kasom/EPOBD2ESP32U8G2/AutoPollingMessages.h

#define NUM_AUTO_POLLING_CAN_MESSAGES 13

can_message_t auto_polling_messages[NUM_AUTO_POLLING_CAN_MESSAGES] = {
  {.flags=0, .identifier=BMS_ID, .data_length_code=8, .data={0x03,0x22,0xb0,0x42,0xaa,0xaa,0xaa,0xaa}}, // HV A
  {.flags=0, .identifier=BMS_ID, .data_length_code=8, .data={0x03,0x22,0xb0,0x43,0xaa,0xaa,0xaa,0xaa}}, // HV V
  {.flags=0, .identifier=BMS_ID, .data_length_code=8, .data={0x03,0x22,0xb0,0x46,0xaa,0xaa,0xaa,0xaa}}, // SoC
  {.flags=0, .identifier=BMS_ID, .data_length_code=8, .data={0x03,0x22,0xb0,0x48,0xaa,0xaa,0xaa,0xaa}}, // Charging status
  {.flags=0, .identifier=BMS_ID, .data_length_code=8, .data={0x03,0x22,0xb0,0x5c,0xaa,0xaa,0xaa,0xaa}}, // Batt temp A/2-40
  {.flags=0, .identifier=BMS_ID, .data_length_code=8, .data={0x03,0x22,0xb0,0x61,0xaa,0xaa,0xaa,0xaa}}, // SoH
  {.flags=0, .identifier=VCU_ID, .data_length_code=8, .data={0x03,0x22,0xb9,0x00,0xaa,0xaa,0xaa,0xaa}}, // Gear
  {.flags=0, .identifier=VCU_ID, .data_length_code=8, .data={0x03,0x22,0xb5,0x83,0xaa,0xaa,0xaa,0xaa}}, // DC-DC A
  {.flags=0, .identifier=VCU_ID, .data_length_code=8, .data={0x03,0x22,0xb5,0x84,0xaa,0xaa,0xaa,0xaa}}, // DC-DC V
  {.flags=0, .identifier=VCU_ID, .data_length_code=8, .data={0x03,0x22,0xb5,0x87,0xaa,0xaa,0xaa,0xaa}}, // DC-DC T
  {.flags=0, .identifier=VCU_ID, .data_length_code=8, .data={0x03,0x22,0xb3,0x09,0xaa,0xaa,0xaa,0xaa}}, // Motor coolant T
  {.flags=0, .identifier=VCU_ID, .data_length_code=8, .data={0x03,0x22,0xb4,0x05,0xaa,0xaa,0xaa,0xaa}}, // Motor T
  {.flags=0, .identifier=VCU_ID, .data_length_code=8, .data={0x03,0x22,0xe1,0x01,0xaa,0xaa,0xaa,0xaa}}, // Odometer
};
